ils15/TwoTreesSk1/Klipper/sanity_checks.cfg

[gcode_macro CHECK_TEMPERATURES]
gcode:
    {% set extruder_temp = printer.extruder.temperature %}
    {% set bed_temp = printer.heater_bed.temperature %}
    {% if extruder_temp < 160 or extruder_temp > 300 %}
        M117 "Extruder temperature out of safe range!"
        M112 ; Emergency stop
    {% endif %}
    {% if bed_temp < 0 or bed_temp > 120 %}
        M117 "Bed temperature out of safe range!"
        M112 ; Emergency stop
    {% endif %}
    M117 "Temperatures OK."

[gcode_macro CHECK_ENDSTOPS]
gcode:
    M117 "Checking Endstops..."
    M18 ; Disable motors
    G4 P500 ; Pause for stability
    QUERY_ENDSTOPS ; Command to check endstop state

[gcode_macro CHECK_HOMING]
gcode:
    G28 ; Home all axes
    {% if printer.toolhead.position.x != 0 or printer.toolhead.position.y != 0 or printer.toolhead.position.z != 0 %}
        M117 "Homing error! Check configuration."
        M112 ; Emergency stop
    {% else %}
        M117 "Homing OK."
    {% endif %}

[gcode_macro CHECK_BED_MESH]
gcode:
    BED_MESH_PROFILE LOAD=default
    {% if not printer.configfile.settings['bed_mesh'].points %}
        M117 "Error: Bed mesh not calibrated!"
        M112 ; Emergency stop
    {% else %}
        M117 "Bed mesh OK."
    {% endif %}

[gcode_macro CHECK_FILAMENT]
gcode:
    M117 "Checking filament..."
    {% if printer.filament_switch_sensor %}
        {% if not printer.filament_switch_sensor.filament_detected %}
            M117 "Error: No filament detected!"
            M112 ; Emergency stop
        {% else %}
            M117 "Filament OK."
        {% endif %}
    {% else %}
        M117 "No filament sensor configured."
    {% endif %}

[gcode_macro CHECK_PRESSURE_ADVANCE]
gcode:
    {% if printer.extruder.pressure_advance < 0.02 or printer.extruder.pressure_advance > 1.0 %}
        M117 "Warning: Unusual pressure advance value!"
    {% else %}
        M117 "Pressure advance settings OK."
    {% endif %}

[gcode_macro CHECK_MOTORS]
gcode:
    M117 "Testing motors..."
    G90 ; Absolute positioning
    G1 X10 Y10 F3000
    G1 X0 Y0 F3000
    M117 "Motors movement test OK."

[gcode_macro PRE_PRINT_CHECKS]
gcode:
    CHECK_TEMPERATURES
    CHECK_ENDSTOPS
    CHECK_FILAMENT
    CHECK_HOMING
    CHECK_BED_MESH
    CHECK_PRESSURE_ADVANCE
    CHECK_MOTORS
    M117 "All checks passed. Ready to print."
